oldgerman/D1-mini-Plus-V1.0/Eagle Pcb project/D1miniPlus__Layout.png

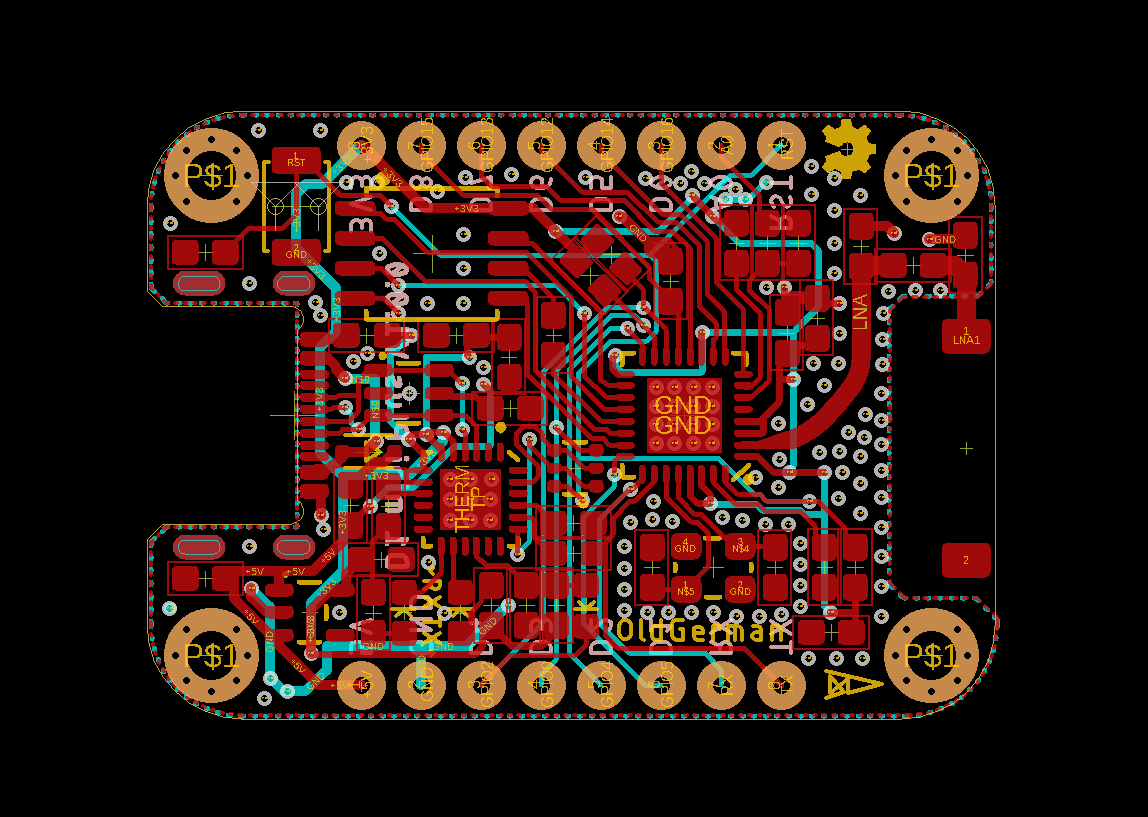
Eagle Pcb project/D1miniPlus__Layout.png
