oldgerman/D1-mini-Plus-V1.0/images/D1miniPlusV1.jpg

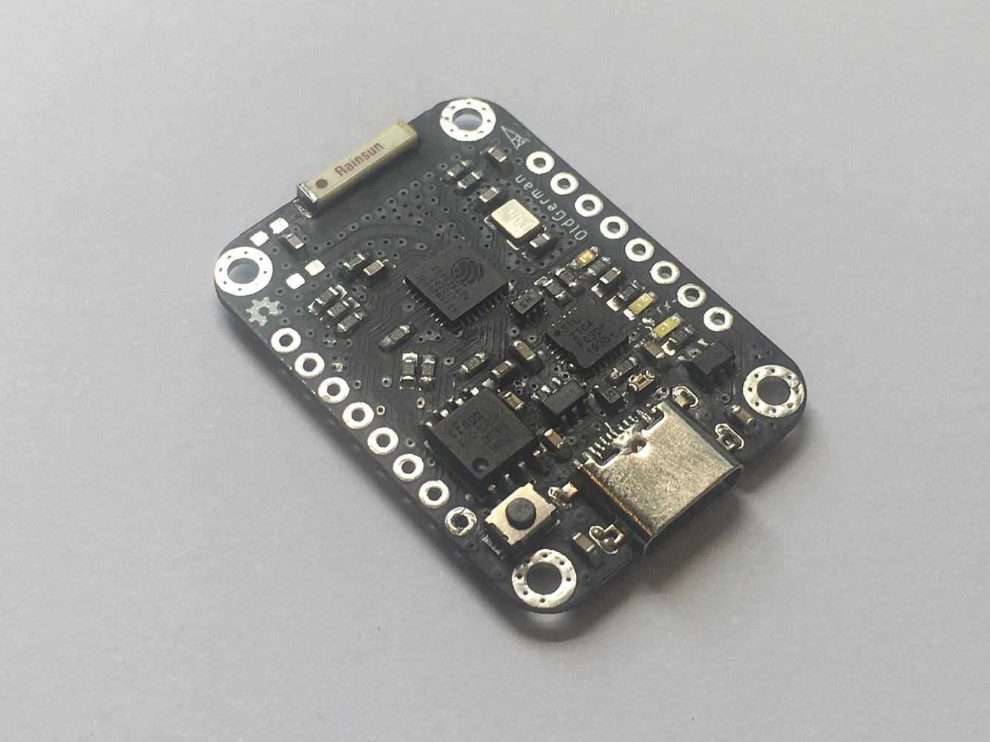
images/D1miniPlusV1.jpg
