oldgerman/D1-mini-Plus-V1.0/images/pcbView.jpg

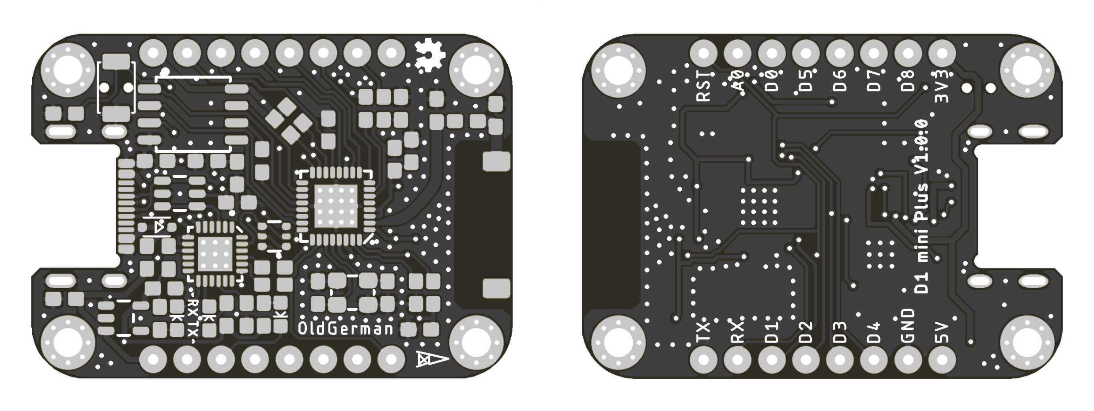
images/pcbView.jpg
